ondras12345/electronic-load/electronic-load-controller/sim/pwm.asc

C1: cap; 1µ
C2: cap; 100n
D1: diode; 1N4148
M1: nmos; BSS145
M2: pmos; BSS84
R1: res; 10k
R2: res; 10k
R3: res; 2k2
R4: res; 100
R5: res; 1k
R6: res; 1k
R7: res; 1k
V1: voltage; 2.5
V2: voltage; PULSE(0 5 0 0 0 {256u*duty} 256u)
V3: voltage; 5
Named nets: 0
TODO wrong nfet
.tran 100m
.step param duty list 0.1 0.2 0.3 0.4 0.5 0.6 0.7 0.8 0.9 0.95 0.99 1.0
